wadhwat/socet-1-shot-clock/KiCad_Files/ShotClockPCB/17pinPCB/17pinPCB.kicad_sch

## KiCad design KiCad_Files/ShotClockPCB/17pinPCB/17pinPCB.kicad_sch (2026-04-19, an earlier design)

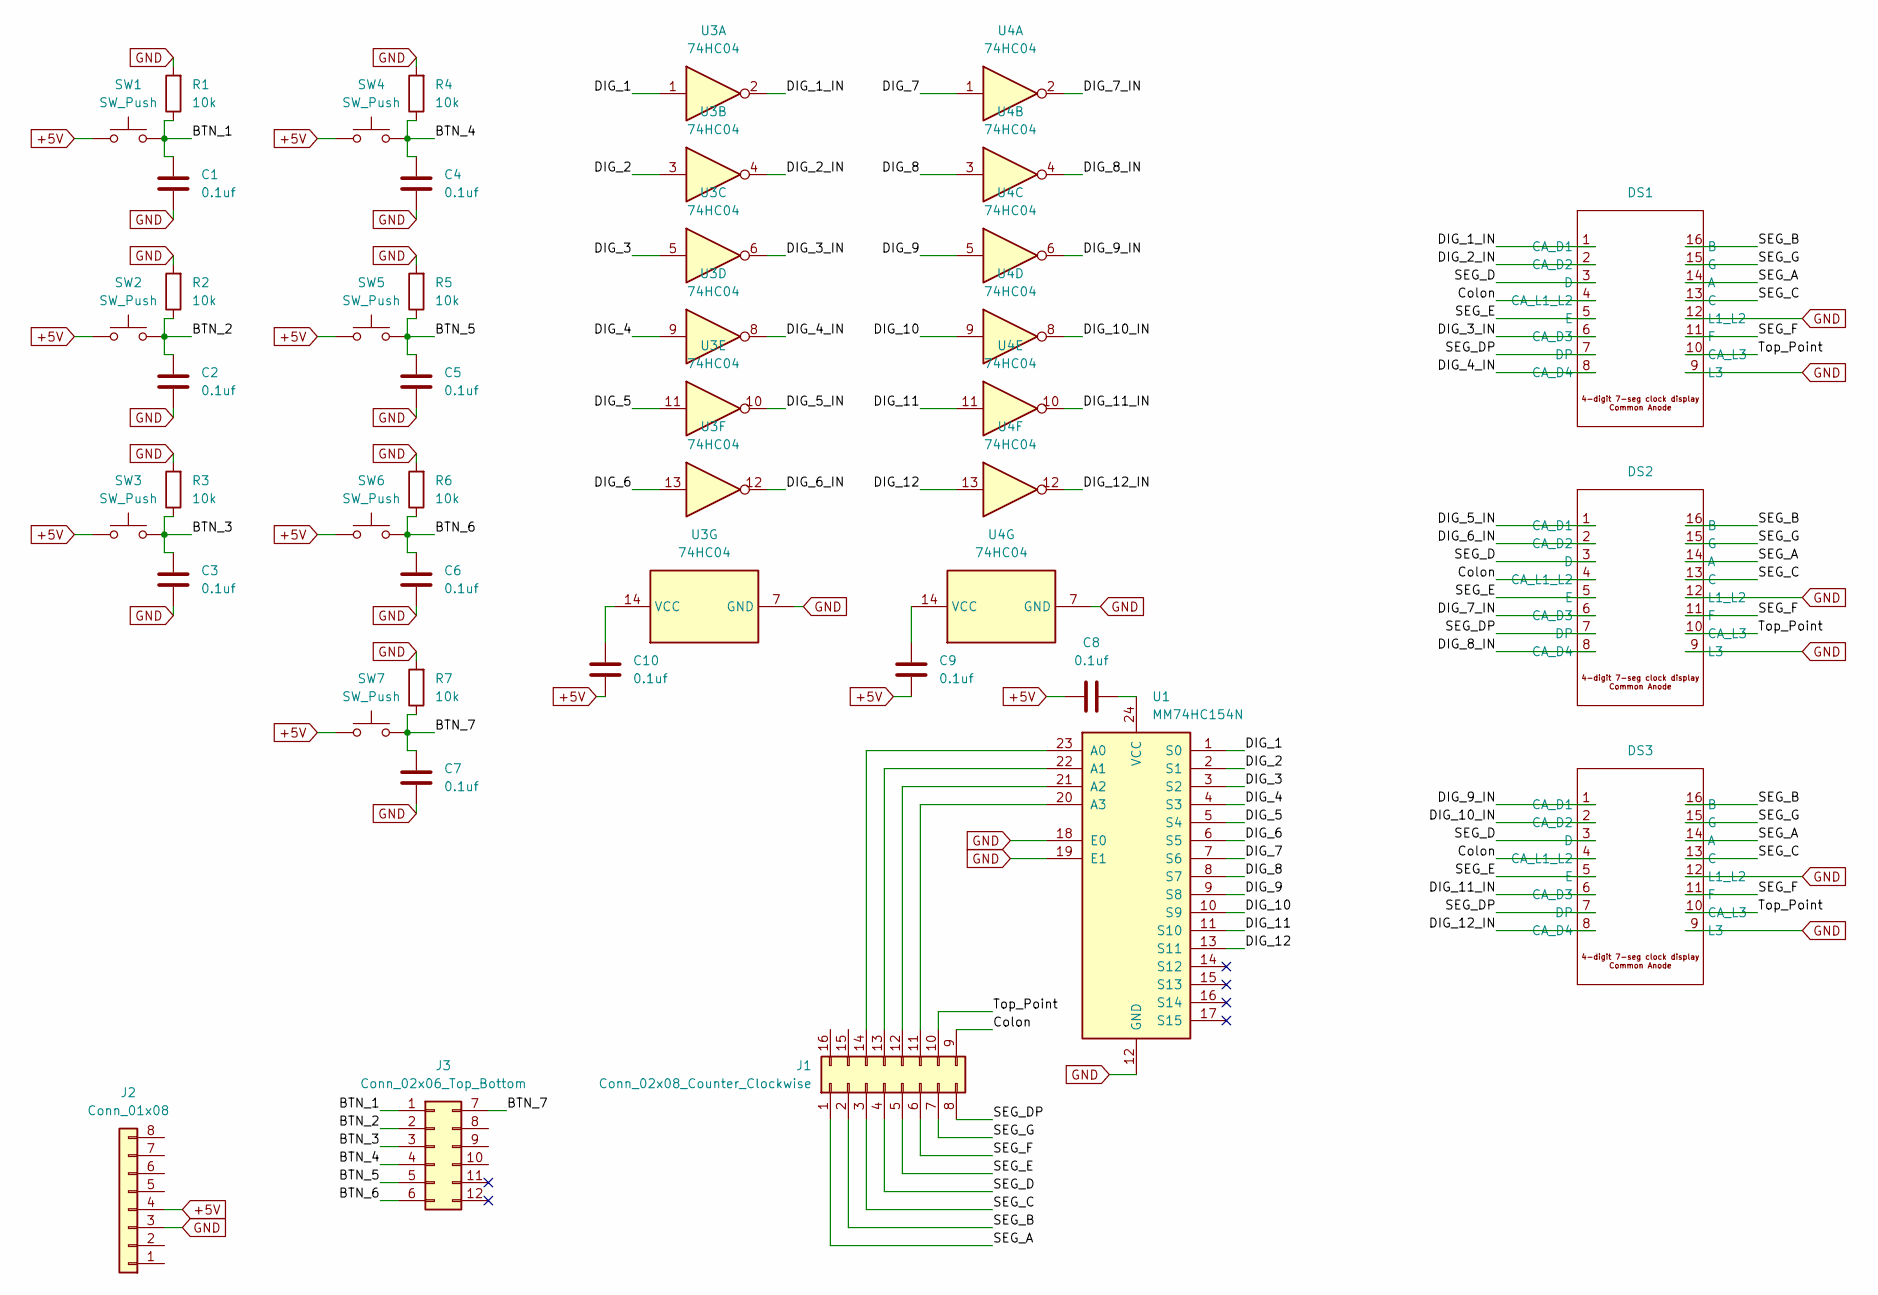
[picture p4: schematic 17pinPCB.kicad_sch]

Parts:
C1, C2, C3, C4, C5, C6, C7, C8, C9, C10: 0.1uf
DS1, DS2, DS3: TDG1050M
J1: Conn_02x08_Counter_Clockwise; PinHeader_2x08_P2.54mm_Vertical
J2: Conn_01x08; PinHeader_1x08_P2.54mm_Vertical
J3: Conn_02x06_Top_Bottom
R1, R2, R3, R4, R5, R6, R7: 10k
SW1, SW2, SW3, SW4, SW5, SW6, SW7: SW_Push; SW_PUSH_6mm_H8.5mm
U1: MM74HC154N; DIP-24_W7.62mm
U3, U4: 74HC04; DIP-14_W7.62mm

Connections:
+5V: C8.2, C9.1, C10.2, J2.4, SW1.1, SW2.1, SW3.1, SW4.1, SW5.1, SW6.1, SW7.1
BTN_1: C1.2, J3.1, R1.1, SW1.2
BTN_2: C2.2, J3.2, R2.1, SW2.2
BTN_3: C3.2, J3.3, R3.1, SW3.2
BTN_4: C4.2, J3.4, R4.1, SW4.2
BTN_5: C5.2, J3.5, R5.1, SW5.2
BTN_6: C6.2, J3.6, R6.1, SW6.2
BTN_7: C7.2, J3.7, R7.1, SW7.2
Colon: DS1.4 (CA_L1_L2), DS2.4 (CA_L1_L2), DS3.4 (CA_L1_L2), J1.9
DIG_1: U1.1 (S0), U3.1
DIG_1_IN: DS1.1 (CA_D1), U3.2
DIG_2: U1.2 (S1), U3.3
DIG_2_IN: DS1.2 (CA_D2), U3.4
DIG_3: U1.3 (S2), U3.5
DIG_3_IN: DS1.6 (CA_D3), U3.6
DIG_4: U1.4 (S3), U3.9
DIG_4_IN: DS1.8 (CA_D4), U3.8
DIG_5: U1.5 (S4), U3.11
DIG_5_IN: DS2.1 (CA_D1), U3.10
DIG_6: U1.6 (S5), U3.13
DIG_6_IN: DS2.2 (CA_D2), U3.12
DIG_7: U1.7 (S6), U4.1
DIG_7_IN: DS2.6 (CA_D3), U4.2
DIG_8: U1.8 (S7), U4.3
DIG_8_IN: DS2.8 (CA_D4), U4.4
DIG_9: U1.9 (S8), U4.5
DIG_9_IN: DS3.1 (CA_D1), U4.6
DIG_10: U1.10 (S9), U4.9
DIG_10_IN: DS3.2 (CA_D2), U4.8
DIG_11: U1.11 (S10), U4.11
DIG_11_IN: DS3.6 (CA_D3), U4.10
DIG_12: U1.13 (S11), U4.13
DIG_12_IN: DS3.8 (CA_D4), U4.12
GND: C1.1, C2.1, C3.1, C4.1, C5.1, C6.1, C7.1, DS1.9 (L3), DS1.12 (L1_L2), DS2.9 (L3), DS2.12 (L1_L2), DS3.9 (L3), DS3.12 (L1_L2), J2.3, R1.2, R2.2, R3.2, R4.2, R5.2, R6.2, R7.2, U1.12 (GND), U1.18 (E0), U1.19 (E1), U3.7 (GND), U4.7 (GND)
unnamed: C8.1, U1.24 (VCC)
unnamed: C9.2, U4.14 (VCC)
unnamed: C10.1, U3.14 (VCC)
unnamed: J1.11, U1.20 (A3)
unnamed: J1.12, U1.21 (A2)
unnamed: J1.13, U1.22 (A1)
unnamed: J1.14, U1.23 (A0)
SEG_A: DS1.14 (A), DS2.14 (A), DS3.14 (A), J1.1
SEG_B: DS1.16 (B), DS2.16 (B), DS3.16 (B), J1.2
SEG_C: DS1.13 (C), DS2.13 (C), DS3.13 (C), J1.3
SEG_D: DS1.3 (D), DS2.3 (D), DS3.3 (D), J1.4
SEG_DP: DS1.7 (DP), DS2.7 (DP), DS3.7 (DP), J1.8
SEG_E: DS1.5 (E), DS2.5 (E), DS3.5 (E), J1.5
SEG_F: DS1.11 (F), DS2.11 (F), DS3.11 (F), J1.6
SEG_G: DS1.15 (G), DS2.15 (G), DS3.15 (G), J1.7
Top_Point: DS1.10 (CA_L3), DS2.10 (CA_L3), DS3.10 (CA_L3), J1.10
