wadhwat/socet-1-shot-clock/sv/src/top.sv

/*
Basketball Shot Clock Top Module

MISSING shot clock driver, shot clock
*/

module top #(
    parameter logic [6:0] BUZZER_LENGTH = 7'd20, //2 seconds long
    parameter integer TIMER_WIDTH = 16
)(
    input  logic clk,                // 100 MHz onboard oscillator
    input  logic rst_in,           // active-high reset input
    // n_rst is equivalent to btn_reset (pb[5])

    input  logic btn_start_stop_raw,     // pb[0]
    input  logic btn_possession_raw,     // pb[1]
    input  logic btn_score_up_raw,       // pb[2]
    input  logic btn_score_down_raw,     // pb[3]
    input  logic btn_shot_reset_raw,     // pb[4]

    //Non SS Outputs
    output logic [3:0] period_leds,
    output logic [1:0] possession_leds,
    output logic buzzer_drive,

    //SS Outputs
    output logic [3:0] display_select,
    output logic [7:0] display_segments,

    output logic colon_out, //Shared colon net on PCB

    output logic gc_colon_out,
    output logic sc_colon_out,
    output logic scr_colon_out
);

    logic n_rst;

    assign n_rst = ~rst_in;

    assign colon_out = 1'b1;

    logic tick_10Hz, tick_1kHz, tick_2640Hz;
    logic btn_start_stop, btn_possession, btn_score_up, btn_score_down, btn_shot_reset;
    logic home_led_wire, away_led_wire;
    logic [3:0] period_led_wire;
    logic [7:0] gc_ss1, gc_ss2, gc_ss3, gc_ss4;
    logic [7:0] sc_ss1, sc_ss2, sc_ss3, sc_ss4;
    logic [7:0] scr_ss1, scr_ss2, scr_ss3, scr_ss4; 
    logic gc_colon_wire, sc_colon_wire;
    logic possession_state_wire;
    logic [1:0] period_state_wire;
    logic [7:0] home_score_wire, away_score_wire;
    logic buzzer_drive_wire;
    logic game_clock_expired_wire;
    logic buzzer_trigger_wire;
    logic period_increment_wire;
    logic possession_increment_wire;
    logic shot_clock_en_wire;
    logic shot_clock_load_wire;
    logic [TIMER_WIDTH-1:0] shot_clock_load_value_wire;
    logic [TIMER_WIDTH-1:0] shot_clock_time_wire;
    logic game_clock_en_wire;
    logic game_clock_load_wire;
    logic [TIMER_WIDTH-1:0] game_clock_load_value_wire;
    logic [TIMER_WIDTH-1:0] game_clock_time_wire;
    logic game_clock_below_10_wire;

    main_driver m1 (
        .clk(clk),
        .tick_2640Hz(tick_2640Hz),
        .n_rst(n_rst),
        .period_led(period_led_wire),
        .home_led(home_led_wire),
        .away_led(away_led_wire),
        .gc_ss1(gc_ss1), .gc_ss2(gc_ss2), .gc_ss3(gc_ss3), .gc_ss4(gc_ss4), //COMPLETE
        .gc_colon(gc_colon_wire),
        .scr_ss1(scr_ss1), .scr_ss2(scr_ss2), .scr_ss3(scr_ss3), .scr_ss4(scr_ss4),
        .scr_colon('0), 
        .sc_ss1(sc_ss1), .sc_ss2(sc_ss2), .sc_ss3(sc_ss3), .sc_ss4(sc_ss4),
        .sc_colon(sc_colon_wire),
        .buzzer_in(buzzer_drive_wire),

        .main_segments_pin_out(display_segments),
        .decoder_pin(display_select),
        .gc_colon_out(gc_colon_out),
        .sc_colon_out(sc_colon_out), 
        .scr_colon_out(scr_colon_out),
        .period_led_out(period_leds), 
        .pos_led_out(possession_leds),
        .buzzer_out(buzzer_drive)
    );

    clock_driver #(
        .TIMER_WIDTH(TIMER_WIDTH)
    ) gcd (
        .raw_deciseconds(game_clock_time_wire),
        
        .seg3(gc_ss1), .seg2(gc_ss2), .seg1(gc_ss3), .seg0(gc_ss4), //COMPLETE to main driver
        .colon(gc_colon_wire)
    );

    clock #(
        .PERIOD_MINUTES(15),
        .SECONDS_PER_MINUTE(60),
        .TENTHS_PER_SECOND(10),
        .TIMER_WIDTH(TIMER_WIDTH)
    ) gc1 (
        .clk(clk),
        .nrst(n_rst),
        .tick_10hz(tick_10Hz),
        .enable(game_clock_en_wire),
        .clock_load(game_clock_load_wire),
        .clock_load_value(game_clock_load_value_wire),
        
        .current_time_value(game_clock_time_wire),
        .expired(game_clock_expired_wire)
    );


    clock_driver #(
        .TIMER_WIDTH(TIMER_WIDTH)
    ) scd (
        .raw_deciseconds(shot_clock_time_wire),
        
        .seg3(sc_ss1), .seg2(sc_ss2), .seg1(sc_ss3), .seg0(sc_ss4), //COMPLETE to main driver
        .colon(sc_colon_wire)
    );

    clock #(
        .PERIOD_MINUTES(0.5), // 30 seconds
        .SECONDS_PER_MINUTE(60),
        .TENTHS_PER_SECOND(10),
        .TIMER_WIDTH(TIMER_WIDTH)
    ) sc1 (
        .clk(clk),
        .nrst(n_rst),
        .tick_10hz(tick_10Hz),
        .enable(shot_clock_en_wire),
        .clock_load(shot_clock_load_wire),
        .clock_load_value(shot_clock_load_value_wire),
        
        .current_time_value(shot_clock_time_wire),
        .expired(shot_clock_expired_wire)
    );

    buzzer_driver #(
        .FREQUENCY(2000), // 2 kHz tone
        .CLK_FREQ(100_000_000) // 100 MHz clock
    ) bd1 (
        .clk(clk),
        .n_rst(n_rst),
        .buzzer_pulse(buzzer_trigger_wire),
        .buzzer_length(BUZZER_LENGTH), //Parameter set at top of top.sv
        .buzzer_out(buzzer_drive_wire)
    );

    score_driver sd1 (
        .home_score(home_score_wire), 
        .away_score(away_score_wire), 
        .scr_ss1(scr_ss1),
        .scr_ss2(scr_ss2),
        .scr_ss3(scr_ss3),
        .scr_ss4(scr_ss4)
    );

    score_tracker st1 (
        .clk(clk),
        .nrst(n_rst),
        .plus_one_possession_pulse(btn_score_up),
        .minus_one_possession_pulse(btn_score_down),
        .possession_state(possession_state_wire), // Assuming home 0
        .home_score(home_score_wire), 
        .away_score(away_score_wire) 
    );

    possession_ctrl pc1 (  //Is a driver as well already technically so...
        .clk(clk),
        .n_rst(n_rst),
        .possession_toggle_pulse(possession_increment_wire),
        .possession_state(possession_state_wire), 
        .home_led(home_led_wire),
        .away_led(away_led_wire)
    );

    period_ctrl pc2 (
        .clk(clk),
        .n_rst(n_rst),
        .increment(period_increment_wire),
        .period_state(period_state_wire),
        .period_leds(period_led_wire)
    );

    control_fsm #(
        .N_BUTTONS(5),
        .TIMER_WIDTH(TIMER_WIDTH),
        .SHOT_TIMER_WIDTH(TIMER_WIDTH),
        .FULL_PERIOD_MINUTES(15)
    ) cfsm1 (
        .clk(clk),
        .n_rst(n_rst),
        .period_state(period_state_wire),
        .shot_clock_expired(shot_clock_expired_wire),
        .game_clock_expired(game_clock_expired_wire),
        .tick_10hz(tick_10Hz),
        .conditioned_buttons({btn_shot_reset, btn_score_down, btn_score_up, btn_possession, btn_start_stop}),
        .buzzer_trigger(buzzer_trigger_wire),
        .period_increment(period_increment_wire),
        .possession_increment(possession_increment_wire),
        .shot_clock_en(shot_clock_en_wire),
        .shot_clock_load(shot_clock_load_wire),
        .shot_clock_load_value(shot_clock_load_value_wire),
        .game_clock_en(game_clock_en_wire),
        .game_clock_load(game_clock_load_wire),
        .game_clock_load_value(game_clock_load_value_wire)
    );

    tick_generator #(
        .CLK_FREQ_HZ(100_000_000), // 100 MHz clock
        .TICK_FREQ_HZ(10),         // 10 Hz tick for period changes
        .TICK_2640_HZ(2640),      // 2,640 Hz tick for shot clock
        .CONDITIONED(1_000)       // 1,000 Hz tick for score updates and shot clock
    ) tg (
        .clk(clk),
        .rst_n(n_rst),
        .tick_10Hz(tick_10Hz),
        .tick_1kHz(tick_1kHz),
        .tick_2640Hz(tick_2640Hz)
    );

    button_conditioner #(
        .N_BUTTONS(5),
        .STREAK_REQUIRED(6)
    ) bc1 (
        .clk(clk),
        .n_rst(n_rst),
        .tick_1kHz(tick_1kHz),
        .raw_buttons({ btn_shot_reset_raw, btn_score_down_raw, btn_score_up_raw, btn_possession_raw, btn_start_stop_raw}),
        .conditioned_buttons( {btn_shot_reset, btn_score_down, btn_score_up, btn_possession, btn_start_stop} )
    );


endmodule
