wadhwat/socet-1-shot-clock/sv/src/clock.sv

// Game period countdown in tenths of a second; decrements on tick_10hz when enabled.

module clock #(
    parameter real    PERIOD_MINUTES      = 12,
    parameter integer SECONDS_PER_MINUTE  = 60,
    parameter integer TENTHS_PER_SECOND   = 10,
    parameter integer TIMER_WIDTH         = 14
) (
    input  wire                        clk,
    input  wire                        nrst,
    input  wire                        tick_10hz,
    input  wire                        enable,
    input  wire                        clock_load,
    input  wire [TIMER_WIDTH-1:0]      clock_load_value,
    output logic [TIMER_WIDTH-1:0]     current_time_value,
    output logic                       expired
);

    localparam integer FULL_PERIOD_TENTHS =
        PERIOD_MINUTES * SECONDS_PER_MINUTE * TENTHS_PER_SECOND;

    logic [TIMER_WIDTH-1:0] time_left_tenths;

    always_ff @(posedge clk or negedge nrst) begin
        if (!nrst) begin
            time_left_tenths <= TIMER_WIDTH'(FULL_PERIOD_TENTHS);
            expired <= 1'b0;
        end else if (clock_load) begin
            time_left_tenths <= clock_load_value;
            expired <= enable && (clock_load_value == '0);
        end else begin
            expired <= (enable && tick_10hz && (time_left_tenths == 1));
            if (enable && tick_10hz && (time_left_tenths != 0))
                time_left_tenths <= time_left_tenths - 1'b1;
        end
    end

    assign current_time_value = time_left_tenths;

endmodule
