wadhwat/socet-1-shot-clock/sv/src/score_tracker.sv

module score_tracker(
    input logic clk,
    input logic nrst,
    input logic plus_one_possession_pulse,
    input logic minus_one_possession_pulse,
    input logic possession_state, // 1 is the away team and 0 is the home team
    output logic [7:0] home_score,
    output logic [7:0] away_score
);

    // Keep internal state at the full 8-bit range; score_driver indicates
    // display overflow for values above 99.
    localparam logic [7:0] MAX_SCORE = 8'd255;

    always_ff @(posedge clk or negedge nrst) begin
        if (!nrst) begin
            home_score <= 8'd0;
            away_score <= 8'd0;
        end
        else if (plus_one_possession_pulse) begin
            if (possession_state) begin
                if (away_score < MAX_SCORE)
                    away_score <= away_score + 8'd1;
                else
                    away_score <= MAX_SCORE; // saturate at MAX_SCORE
            end else begin
                if (home_score < MAX_SCORE)
                    home_score <= home_score + 8'd1;
                else
                    home_score <= MAX_SCORE; // saturate at MAX_SCORE
            end
        end
        else if (minus_one_possession_pulse) begin
            if (possession_state) begin
                if (away_score != 8'd0)
                    away_score <= away_score - 8'd1;
            end
            else begin
                if (home_score != 8'd0)
                    home_score <= home_score - 8'd1;
            end
        end
    end

endmodule
